marinstef6/TSC-proiect/Images/ecran-2d.jpg

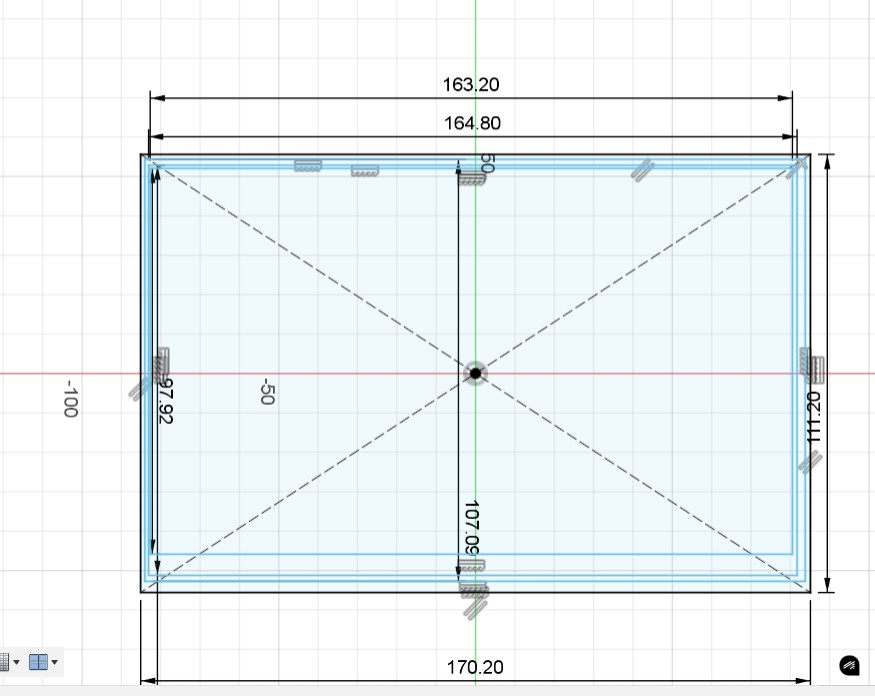
Images/ecran-2d.jpg
