marinstef6/TSC-proiect/Images/pcb_3d.jpg

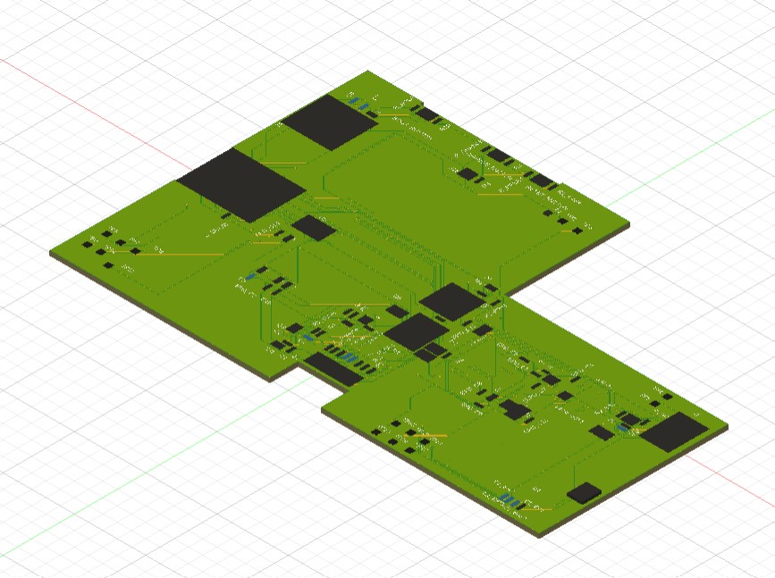
Images/pcb_3d.jpg
